nanosatlab/xbandtransceiver/TestBoards/PLL_LMX2572/SW/LMX2572/Core/Src/main.c

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
/* Includes ------------------------------------------------------------------*/
#include "main.h"

/* USER CODE BEGIN Includes */
#include "lmx2572.h"
/* USER CODE END Includes */

SPI_HandleTypeDef hspi1;

UART_HandleTypeDef huart2;

void SystemClock_Config(void);
static void MX_GPIO_Init(void);
static void MX_USART2_UART_Init(void);
static void MX_SPI1_Init(void);
/**
  * @brief  The application entry point.
  * @retval int
  */
int main(void)
{
  /* MCU Configuration--------------------------------------------------------*/

  /* Reset of all peripherals, Initializes the Flash interface and the Systick. */
  HAL_Init();

  /* Configure the system clock */
  SystemClock_Config();

  /* Initialize all configured peripherals */
  MX_GPIO_Init();
  MX_USART2_UART_Init();
  MX_SPI1_Init();
  /* USER CODE BEGIN 2 */
  PLL mypll;

  // Test upon connection (5200 MHz)
  HAL_GPIO_WritePin(GPIOA, GPIO_PIN_8, GPIO_PIN_SET);		// Tx_CE HIGH
  HAL_GPIO_WritePin(GPIOB, GPIO_PIN_5, GPIO_PIN_SET);		// LO_EN HIGH
  mypll = LMX2572_defaultConfig(mypll);
  LMX2572_load_regs(&hspi1);

  LMX2572_switchOff_RFoutA(mypll);

  mypll = LMX2572_frequency(mypll, &hspi1, 5800);

  LMX2572_switchOn_RFoutA(mypll);

  /* USER CODE END 2 */

  /* Infinite loop */
  /* USER CODE BEGIN WHILE */
  while (1)
  {
    /* USER CODE END WHILE */
	  for(float f=5600; f<6000; f++){
		  HAL_Delay(100);
//		  LMX2572_switchOff_RFoutA(mypll);
		  mypll = LMX2572_frequency(mypll, &hspi1, f);
//		  LMX2572_switchOn_RFoutA(mypll);
	  }

    /* USER CODE BEGIN 3 */
  }
  /* USER CODE END 3 */
}

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
